c4deszes/sense/software/docs/software.adoc

= Software domain overview

== Software Requirements

- xref:requirements/communication.adoc[Communication requirements]
- xref:requirements/diagnostics.adoc[Diagnostic requirements]
- xref:requirements/memory.adoc[Memory requirements]
- xref:requirements/power.adoc[Power requirements]
- xref:requirements/sensor.adoc[Sensor requirements]

== Software Architecture

- xref:architecture/software.adoc[Software architecture]
- xref:architecture/design-alternatives.adoc[Design alternatives]
